JaneliaSciComp/modular_device_enclosure/multiple/5x3x1_3x2x1.dxf

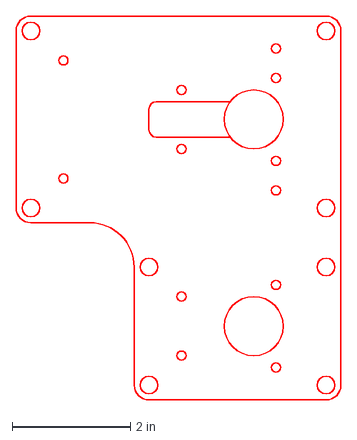
[picture p15: CAD file, 2017-08-10]
multiple/5x3x1_3x2x1.dxf
5.50 x 6.50 in
