JaneliaSciComp/modular_device_enclosure/multiple/5x3x1_3x2x1_lc.dxf

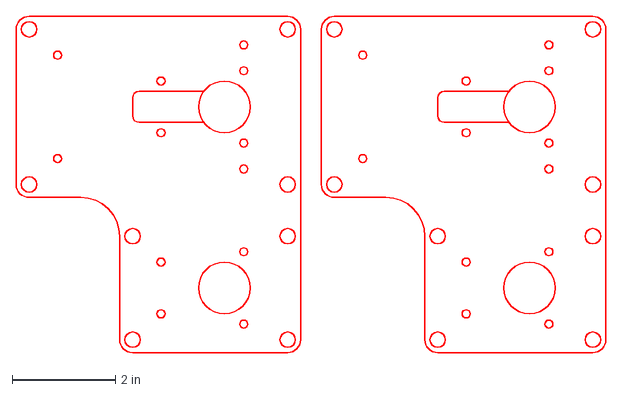
[picture p16: CAD file, 2017-08-10]
multiple/5x3x1_3x2x1_lc.dxf
11.4 x 6.50 in
