JaneliaSciComp/modular_device_enclosure/multiple/5x3x1_3x2x3_lc.dxf

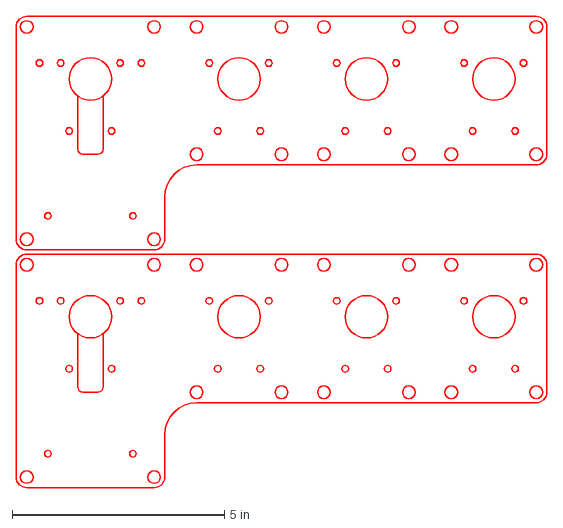
[picture p17: CAD file, 2017-07-06]
multiple/5x3x1_3x2x3_lc.dxf
12.5 x 11.1 in
