JaneliaSciComp/modular_device_enclosure/multiple/5x3x1_3x2x3.dxf

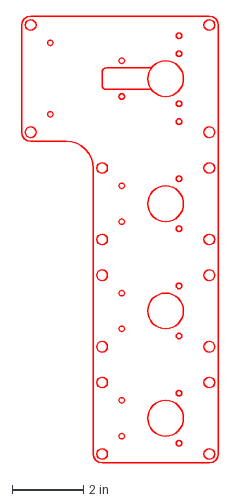
[picture p18: CAD file, 2017-07-06]
multiple/5x3x1_3x2x3.dxf
5.50 x 12.5 in
