JaneliaSciComp/modular_device_enclosure/multiple/5x3x4.dxf

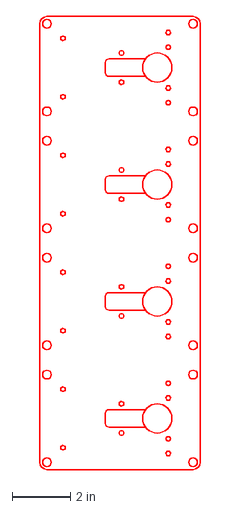
[picture p19: CAD file, 2017-07-06]
multiple/5x3x4.dxf
5.50 x 15.5 in
