JaneliaSciComp/modular_device_enclosure/multiple/5x3x4_lc.dxf

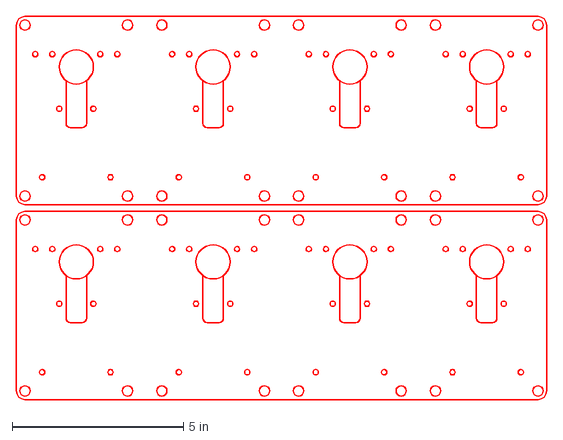
[picture p20: CAD file, 2017-07-06]
multiple/5x3x4_lc.dxf
15.5 x 11.2 in
