JaneliaSciComp/modular_device_enclosure/multiple/5x3x2_lc.dxf

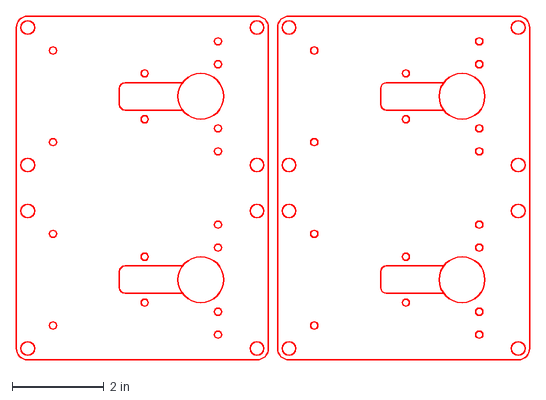
[picture p21: CAD file, 2017-07-06]
multiple/5x3x2_lc.dxf
11.2 x 7.50 in
