JaneliaSciComp/modular_device_enclosure/multiple/5x3x2.dxf

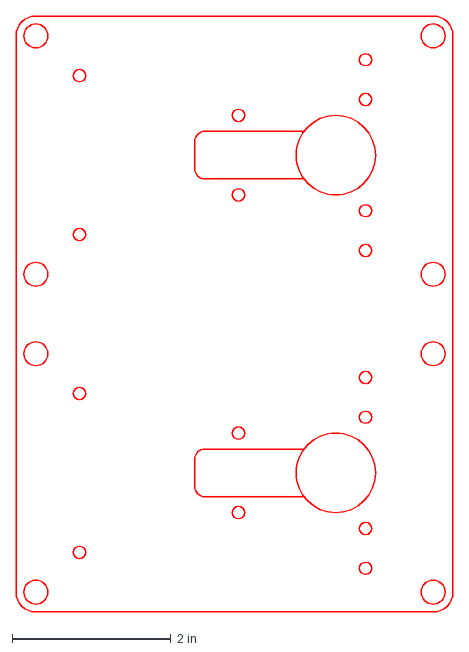
[picture p22: CAD file, 2017-07-06]
multiple/5x3x2.dxf
5.50 x 7.50 in
