JaneliaSciComp/modular_device_enclosure/multiple/5x3x3.dxf

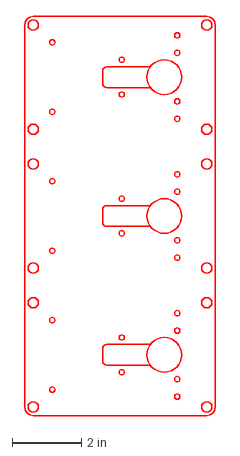
[picture p23: CAD file, 2017-07-06]
multiple/5x3x3.dxf
5.50 x 11.5 in
