JaneliaSciComp/modular_device_enclosure/multiple/3x2x2.dxf

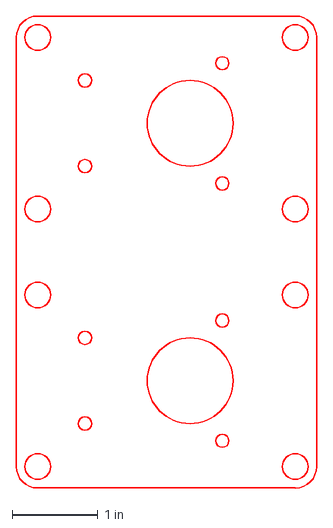
[picture p24: CAD file, 2017-05-04]
multiple/3x2x2.dxf
3.50 x 5.50 in
