JaneliaSciComp/modular_device_enclosure/multiple/3x2x3_lc.dxf

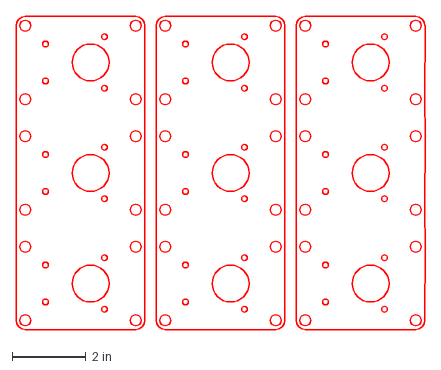
[picture p25: CAD file, 2017-05-04]
multiple/3x2x3_lc.dxf
11.1 x 8.50 in
