JaneliaSciComp/modular_device_enclosure/multiple/3x2x3.dxf

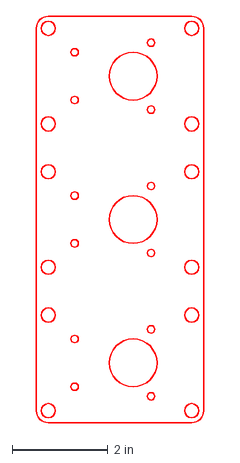
[picture p26: CAD file, 2017-05-04]
multiple/3x2x3.dxf
3.50 x 8.50 in
